Damien130/SixPak_Ultra/Pictures/adlib.png

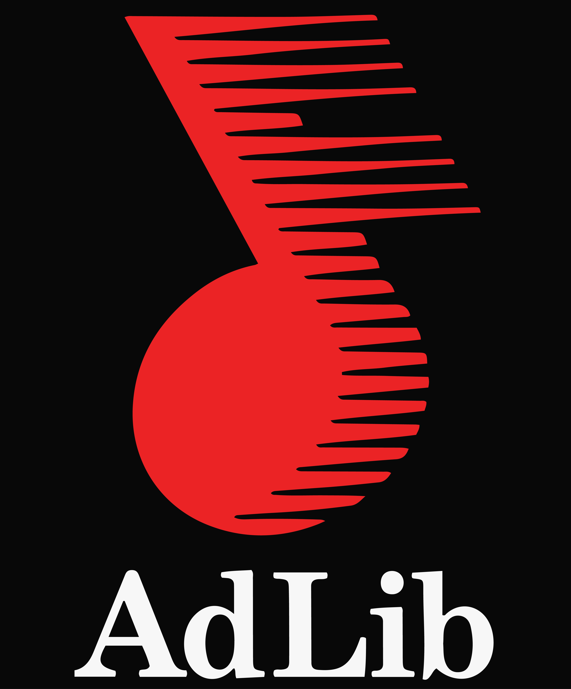
Pictures/adlib.png
